anoff/plantbuddy/esp8266.secrets.template.c

#define WIFI_SSID "network"
#define WIFI_KEY "pasword"
#define POST_URL "http://blup.com/" // make sure this is http and not https of your firebase function
#define HEADER_SECRET "mightysecret" // define the same secret as set for header.secret in the firebase setup
